PanykSystem/gameboy-hifi-audio/firmware/src/audio_pipeline.c

#include "audio_pipeline.h"

#include <stdbool.h>
#include <stdint.h>
#include <stdio.h>
#include <stdlib.h>
#include <string.h>
#include <math.h>

#include "freertos/FreeRTOS.h"
#include "freertos/stream_buffer.h"
#include "freertos/semphr.h"
#include "freertos/task.h"
#include "esp_log.h"
#include "esp_timer.h"

#include "dsps_fft2r.h"     // spectrum tap: esp-dsp radix-2 FFT

#include "i2s_codec.h"
#include "dsp.h"
#include "sfx.h"

#ifndef M_PI
#define M_PI 3.14159265358979323846
#endif

static const char *TAG = "audio";

// 256 stereo frames x 8 bytes/frame = 2 KB per read, ~5.8 ms at 44.1 kHz.
// Frequent small reads keep the producer/consumer relationship tight at the cost
// of more task wakeups per second.
#define READ_FRAMES 256
#define FRAME_BYTES 8                       // I2S input: stereo, 32-bit slots
#define OUT_FRAME_BYTES 4                   // PCM output: stereo, 16-bit

// At 44.1 kHz stereo 16-bit, audio is 176.4 KB/s (~176 bytes/ms). The stream
// buffer absorbs the BT consumer's burst pull pattern (it idles while L2CAP TX
// completes, then grabs a chunk). Sized to hold the ~5 KB natural burst swing
// (observed fill range 1-6 KB) plus a little margin above the high-water mark.
#define PCM_STREAM_BUFFER_BYTES (8 * 1024)     // ~46 ms max; was 12 KB
// High-water trim: the producer skips its push while the queue is already at/above
// this level, so latency stays bounded (~34 ms) instead of drifting toward full as
// the 44.1 kHz producer slowly outruns the sink's consume rate (no rate matching).
// Set above the ~5 KB burst swing so normal bursts aren't clipped -- only the slow
// drift trips it, dropping one ~6 ms block occasionally (rare, ~inaudible) rather
// than letting the fill climb to a 70 ms overflow.
#define PCM_STREAM_HIGH_WATER   (6 * 1024)
// Wake the BT consumer as soon as one SBC-sized block is ready.
// 512 bytes = 128 stereo frames ~2.9 ms.
#define PCM_STREAM_TRIGGER_LEVEL 512

#define MAG_LOG_INTERVAL_US 1000000          // peak log once per second

// On-demand ADC capture for noise-floor / spectrum analysis. audio_pipeline_capture()
// requests N raw samples; the pipeline grabs the next N frames verbatim (no arming, so
// it captures the quiet noise floor, not just loud audio) and dumps them as CSV between
// WAVEDUMP_BEGIN / WAVEDUMP_END markers over UART for tools/plot_wavedump.py. The dump
// printf stalls this real-time task ~1 s, so audio hiccups during a capture (fine for a
// bench measurement; the samples are already grabbed before the dump runs).
//
// The capture buffer is heap-allocated per request (by audio_pipeline_capture, in
// the caller's context) and freed by the pipeline task after the dump. A static
// buffer here would park 8 KB of DRAM for a bench-only feature -- DRAM the SBC
// encoder's 4 KB media buffers need at their tightest (streaming + a BLE config
// client + clip playback ran the heap dry and chopped the stream).
#define WAVEDUMP_MAX 1024                    // 23.2 ms at 44.1 kHz
static volatile int      s_wd_request = 0;   // samples to capture on next read (0 = idle)
static int32_t *volatile s_wd_buf     = NULL; // owned by the in-flight capture

static StreamBufferHandle_t s_pcm_stream = NULL;
// True only while a sink is actively streaming (set from bt_a2d on the media
// state). Gates the producer push so the buffer isn't pre-filled to full while
// idle/connecting. Written from the BT task, read by the pipeline task; a plain
// bool write is atomic on ESP32.
static volatile bool s_bt_streaming = false;

// Prebuffer: at stream start the consumer emits silence until this many bytes have
// queued, so real audio only flows once there's a cushion. Filling from empty
// otherwise underruns for the first ~0.5 s -- each partial read is real samples
// then zero-pad, a discontinuity the SBC encoder renders as garble. ~23 ms at
// 44.1 kHz/16-bit/stereo; small enough to stay low-latency, large enough to cover
// the consumer's bursty pull. Cleared on stop so each connect re-primes.
#define PCM_PRIME_TARGET_BYTES  (4 * 1024)
static volatile bool s_pcm_primed = false;

// Cooperative park (Mode A: stop the digital path so I2S/MCLK can stop).
// audio_pipeline_stop() sets s_park_req; the task acks via s_parked_sem at the
// top of its loop and blocks on a task notification until audio_pipeline_resume()
// wakes it. The task stays alive, so silence/peak window state and buffers
// persist, and I2S is never torn down under an in-flight read.
static TaskHandle_t      s_pipeline_task = NULL;
static SemaphoreHandle_t s_parked_sem    = NULL;
static volatile bool     s_park_req       = false;

// Silence detection state. Threshold is the int32 sample value: the ADC delivers
// 24-in-32 left-justified, so the int32 sample = 24-bit value << 8.
#define SILENCE_THRESHOLD_I32   0x10000
// Consecutive ~1 s below-threshold windows before declaring silence.
#define SILENCE_WINDOWS_TO_QUIET CONFIG_GBHIFI_SILENCE_WINDOWS

static audio_silence_cb_t s_silence_cb = NULL;
static bool s_is_silent = false;
static int  s_silent_window_count = 0;

// ---- spectrum tap ---------------------------------------------------------
// Per-channel rings of the newest post-DSP samples the user is hearing (the local
// speaker/HP program, or the Bluetooth program while a sink streams). The pipeline
// task fills them per block when enabled; audio_pipeline_compute_spectrum() (a
// non-realtime caller) snapshots the last SPEC_FFT_N of each and FFTs them
// independently for a stereo spectrum. Benign torn reads are fine for a
// visualizer, so the rings are lock-free.
#define SPEC_FFT_N    256                 // FFT window (5.8 ms at 44.1 kHz); small on
                                          // purpose to keep DRAM free for BT + BLE
#define SPEC_RING     512                 // >= SPEC_FFT_N, power of two
#define SPEC_MAX_BINS 64                  // per channel
static int16_t           s_spec_l[SPEC_RING];
static int16_t           s_spec_r[SPEC_RING];
static volatile uint32_t s_spec_wr    = 0;
static volatile bool     s_spec_on    = false;
static volatile bool     s_spec_is_bt = false;   // last tapped source: true=BT, false=local

void audio_pipeline_set_silence_cb(audio_silence_cb_t cb)
{
    s_silence_cb = cb;
}

// Load accounting (see audio_pipeline.h). Written only by the pipeline task;
// read + reset by the console. Plain aligned 32-bit accesses are atomic on
// ESP32; the 64-bit accumulator can tear against a concurrent reset, costing at
// worst one bench readout -- acceptable for diagnostics.
static volatile uint64_t s_ld_acc_us  = 0;
static volatile uint32_t s_ld_blocks  = 0;
static volatile uint32_t s_ld_max_us  = 0;
static volatile uint32_t s_ld_over    = 0;

void audio_pipeline_load_stats(audio_load_t *out)
{
    if (!out) return;
    uint32_t blocks = s_ld_blocks;
    out->blocks    = blocks;
    out->avg_us    = blocks ? (uint32_t)(s_ld_acc_us / blocks) : 0;
    out->max_us    = s_ld_max_us;
    out->over      = s_ld_over;
    out->budget_us = (uint32_t)((uint64_t)READ_FRAMES * 1000000u / 44100u);
    s_ld_acc_us = 0;
    s_ld_blocks = 0;
    s_ld_max_us = 0;
    s_ld_over   = 0;
}

void audio_pipeline_capture(int samples)
{
    if (samples <= 0 || samples > WAVEDUMP_MAX) samples = WAVEDUMP_MAX;
    if (s_wd_buf) return;   // a capture is already in flight; ignore
    // Allocated here (console-task context), freed by the pipeline task after
    // the dump. Failing is fine -- wavedump is a bench tool and the heap is
    // deliberately tight while streaming; try again with the stream stopped.
    int32_t *buf = malloc((size_t)samples * 2 * sizeof(int32_t));
    if (!buf) {
        printf("wavedump: not enough free heap (%d frames); stop streaming and retry\n",
               samples);
        return;
    }
    s_wd_buf = buf;
    s_wd_request = samples;
}

void audio_pipeline_spectrum_enable(bool on)
{
    s_spec_on = on;
}

bool audio_pipeline_spectrum_is_bt(void)
{
    return s_spec_is_bt;
}

// FFT one channel's ring snapshot into `nbins` log-spaced 0..255 magnitude bytes.
// `fft`/`hann` are caller-provided scratch/window (sized SPEC_FFT_N).
static void spec_channel(const int16_t *ring, float *fft, const float *hann,
                         uint8_t *out, int nbins)
{
    uint32_t start = s_spec_wr - SPEC_FFT_N;
    for (int i = 0; i < SPEC_FFT_N; i++) {
        float s = (float)ring[(start + i) & (SPEC_RING - 1)] * (1.0f / 32768.0f);
        fft[2 * i]     = s * hann[i];
        fft[2 * i + 1] = 0.0f;
    }
    dsps_fft2r_fc32(fft, SPEC_FFT_N);
    dsps_bit_rev_fc32(fft, SPEC_FFT_N);

    // Fold bins 1..N/2 into nbins log-spaced bands (peak power per band), then map
    // dB to a 0..255 byte. Rough by design -- it's a "cool" meter, not analysis.
    const int   kmax     = SPEC_FFT_N / 2;      // 256
    const float FLOOR_DB = -60.0f;
    for (int b = 0; b < nbins; b++) {
        int lo = (int)floorf(powf((float)kmax, (float)b / nbins));
        int hi = (int)floorf(powf((float)kmax, (float)(b + 1) / nbins));
        if (lo < 1)    lo = 1;
        if (hi <= lo)  hi = lo + 1;
        if (hi > kmax) hi = kmax;
        float peak = 0.0f;
        for (int k = lo; k < hi; k++) {
            float re = fft[2 * k], im = fft[2 * k + 1];
            float p = re * re + im * im;        // power (magnitude^2)
            if (p > peak) peak = p;
        }
        float norm = peak / ((float)kmax * (float)kmax);
        float db   = 10.0f * log10f(norm + 1e-9f);   // 10*log10: norm is power
        int   v    = (int)((db - FLOOR_DB) / (0.0f - FLOOR_DB) * 255.0f);
        if (v < 0)   v = 0;
        if (v > 255) v = 255;
        out[b] = (uint8_t)v;
    }
}

int audio_pipeline_compute_spectrum(uint8_t *bins, int nbins)
{
    if (!s_spec_on || !bins || nbins <= 0) return 0;
    if (nbins > SPEC_MAX_BINS) nbins = SPEC_MAX_BINS;

    static bool  s_ready = false;
    static float s_hann[SPEC_FFT_N];
    static float s_fft[SPEC_FFT_N * 2];         // reused L then R (sequential)
    if (!s_ready) {
        if (dsps_fft2r_init_fc32(NULL, SPEC_FFT_N) != ESP_OK) {
            ESP_LOGW(TAG, "fft init failed; spectrum disabled");
            s_spec_on = false;
            return 0;
        }
        for (int i = 0; i < SPEC_FFT_N; i++)
            s_hann[i] = 0.5f * (1.0f - cosf(2.0f * (float)M_PI * i / (SPEC_FFT_N - 1)));
        s_ready = true;
    }

    spec_channel(s_spec_l, s_fft, s_hann, bins,         nbins);  // L bands
    spec_channel(s_spec_r, s_fft, s_hann, bins + nbins, nbins);  // R bands
    return 2 * nbins;
}

void audio_pipeline_set_bt_streaming(bool streaming)
{
    s_bt_streaming = streaming;
    if (!streaming) s_pcm_primed = false;   // re-prebuffer on the next connect
}

bool audio_pipeline_is_silent(void)
{
    return s_is_silent;
}

static void update_silence(int32_t peak_max)
{
    bool below = (peak_max < SILENCE_THRESHOLD_I32);
    if (below) {
        if (s_silent_window_count < SILENCE_WINDOWS_TO_QUIET) {
            s_silent_window_count++;
        }
        if (!s_is_silent && s_silent_window_count >= SILENCE_WINDOWS_TO_QUIET) {
            s_is_silent = true;
            if (s_silence_cb) s_silence_cb(true);
        }
    } else {
        s_silent_window_count = 0;
        if (s_is_silent) {
            s_is_silent = false;
            if (s_silence_cb) s_silence_cb(false);
        }
    }
}

static void pipeline_task(void *arg)
{
    // The ES8388 ADC emits 24-bit samples in 32-bit I2S slots (32-in-32), so
    // each int32 holds the 24-bit sample value in bits 31:8, zero-pad in 7:0. A
    // sign-extending right-shift by 16 gives a 16-bit signed value, discarding
    // the 8 least-significant bits of resolution.
    static int32_t stereo_buf[READ_FRAMES * 2];     // ADC in: int32 L,R
    static int16_t out_buf[READ_FRAMES * 2];        // BT PCM out: int16 L,R interleaved
    static int16_t local_buf[READ_FRAMES * 2];      // local DAC program: int16 L,R interleaved (stereo)
    static int32_t dac_buf[READ_FRAMES * 2];        // DAC out: int32 L,R (stereo)

    int32_t peak_l = 0, peak_r = 0;
    size_t  fill_min = SIZE_MAX, fill_max = 0;
    int64_t window_start_us = esp_timer_get_time();
    // On-demand capture buffer (filled across reads, one read is only READ_FRAMES).
    // Heap-allocated per capture by audio_pipeline_capture(); freed here after the
    // dump so the 8 KB isn't resident between bench captures.
    int32_t *wd_buf = NULL;
    int wd_have = 0;      // samples captured into the active dump
    int wd_target = 0;    // 0 = not capturing; else samples requested for this dump
    bool bt_streaming_prev = false;   // edge-detect the streaming gate for buffer reset

    while (1) {
        // Cooperative park for Mode A: when stop() requests it, ack and block
        // until resume() notifies us. Done at the loop top so we are not inside
        // i2s_codec_read when the channel is disabled. On wake, I2S has already
        // been restarted by resume(), so fall through to the next read.
        if (s_park_req) {
            s_park_req = false;
            xSemaphoreGive(s_parked_sem);
            ulTaskNotifyTake(pdTRUE, portMAX_DELAY);
            continue;
        }

        size_t bytes_read = 0;
        esp_err_t err = i2s_codec_read(stereo_buf, sizeof(stereo_buf), &bytes_read, 100);
        if (err != ESP_OK) {
            ESP_LOGW(TAG, "i2s read: %s (bytes=%u)",
                     esp_err_to_name(err), (unsigned)bytes_read);
            vTaskDelay(pdMS_TO_TICKS(100));
            continue;
        }

        size_t frames = bytes_read / FRAME_BYTES;
        int64_t work_t0 = esp_timer_get_time();

        // On-demand capture: when a request lands, grab the next wd_target frames
        // verbatim (no arming, so the quiet noise floor is captured as-is), then dump
        // as CSV between markers. printf (not ESP_LOG) so the host parser gets clean
        // lines. The dump stalls this task ~1 s; audio hiccups then recovers.
        if (wd_target == 0 && s_wd_request > 0) {
            wd_target = s_wd_request;
            s_wd_request = 0;
            wd_buf = s_wd_buf;
            wd_have = 0;
        }
        if (wd_target > 0 && wd_buf) {
            for (size_t i = 0; i < frames && wd_have < wd_target; i++) {
                wd_buf[wd_have * 2]     = stereo_buf[i * 2];
                wd_buf[wd_have * 2 + 1] = stereo_buf[i * 2 + 1];
                wd_have++;
            }
            if (wd_have >= wd_target) {
                printf("WAVEDUMP_BEGIN n=%d fs=44100 fmt=24in32\n", wd_target);
                for (int i = 0; i < wd_target; i++) {
                    printf("%ld,%ld\n",
                           (long)wd_buf[i * 2], (long)wd_buf[i * 2 + 1]);
                }
                printf("WAVEDUMP_END\n");
                wd_target = 0;
                free(wd_buf);
                wd_buf = NULL;
                s_wd_buf = NULL;   // capture complete; allow the next request
            }
        }

        // Convert stereo 32-bit slot data to 16-bit interleaved stereo, tracking
        // peaks for the once-per-second magnitude log. The sign-extending
        // right-shift by 16 keeps the 16 most significant bits of the 24-bit
        // sample, discarding the lowest 8 bits of resolution.
        for (size_t i = 0; i < frames; i++) {
            int32_t l = stereo_buf[i * 2];
            int32_t r = stereo_buf[i * 2 + 1];

            int32_t la = (l < 0) ? -l : l;
            int32_t ra = (r < 0) ? -r : r;
            if (la > peak_l) peak_l = la;
            if (ra > peak_r) peak_r = ra;

            int16_t lo = (int16_t)(l >> 16);
            int16_t ro = (int16_t)(r >> 16);
            out_buf[i * 2]     = lo;
            out_buf[i * 2 + 1] = ro;
            // Local program stays stereo. The ES8388 DAC drives the HP amp
            // (LOUT1/ROUT1) directly, which must stay stereo, and the line out
            // (LOUT2/ROUT2) feeds a passive 2-R L+R sum to the mono speaker amp.
            // The speaker mono-down happens in hardware, not here.
            local_buf[i * 2]     = lo;
            local_buf[i * 2 + 1] = ro;
        }

        // Render this block's SFX cue once (advances cue state a single time) so
        // the same samples can be mixed into both the BT and DAC paths.
        sfx_generate_block(frames);

        // BT DSP: source-side noise reduction (HPF/LPF/notch + gate) + optional EQ
        // + digital volume + SFX cue mix, in place on out_buf before the
        // stream-buffer push so the SBC encoder sees the cleaned, gated signal (not
        // the raw capture floor, which SBC renders as audible digital hash).
        //
        // Run it only while a sink is actually streaming: the push below is gated
        // on s_bt_streaming, so outside of streaming the processed buffer is
        // thrown away and the NR chain (a dozen biquad passes since the
        // reconstruction LPF) is pure waste. At 80 MHz that waste was real: it
        // left the boot chime's blocks over budget while the boot-time init
        // storm ran, which chopped the chime. On the idle->streaming edge the BT
        // DSP state (filter delay lines, gate envelope) is stale from the last
        // stream, so reset it for a clean start.
        bool bt_streaming = s_bt_streaming;
        if (bt_streaming) {
            if (!bt_streaming_prev) dsp_bt_reset();
            dsp_process_bt(out_buf, frames);
        }

        // Push the interleaved stereo PCM into the stream buffer for A2DP, but only
        // while a sink is actively streaming. Gating the fill keeps the buffer from
        // pre-filling to full while idle/connecting -- which otherwise hands the SBC
        // encoder a full (~70 ms) buffer at connect that overflows and drops for a
        // second or two. On the streaming->idle edge, empty the buffer so the next
        // connect starts from ~0 latency; the consumer (a2d_data_cb) is idle once the
        // media stops, so the reset does not race a concurrent read. Non-blocking
        // send: if the consumer falls behind, drop rather than stall I2S DMA.
        if (s_pcm_stream && bt_streaming) {
            // High-water trim: skip the push while the queue is already at the mark,
            // so latency stays bounded instead of drifting toward full. Drops the
            // newest ~6 ms block once per drift accumulation (rare) rather than
            // letting the fill climb to an eventual overflow.
            if (xStreamBufferBytesAvailable(s_pcm_stream) < PCM_STREAM_HIGH_WATER) {
                (void)xStreamBufferSend(s_pcm_stream, out_buf,
                                        frames * OUT_FRAME_BYTES, 0);
            }
            size_t fill = xStreamBufferBytesAvailable(s_pcm_stream);
            if (fill < fill_min) fill_min = fill;
            if (fill > fill_max) fill_max = fill;
        } else if (s_pcm_stream && bt_streaming_prev && !bt_streaming) {
            xStreamBufferReset(s_pcm_stream);   // streaming ended: drop stale audio
        }
        // (bt_streaming_prev is updated at the end of the loop iteration: the
        // DAC-zeroing block below also needs to see the idle->streaming edge.)

        // Local DSP: stereo speaker EQ, digital volume, SFX cue mix, saturate,
        // in place on the interleaved local buffer.
        //
        // Skipped entirely while a sink streams: STREAMING and local playback are
        // mutually exclusive (the state machine mutes the speaker amp for the whole
        // stream, and a wired HP plug suspends A2DP), so the local program is
        // computed only to be played into muted/disconnected outputs. At 80 MHz
        // that waste is what starves core 0's SBC encoder of its escape hatch:
        // dropping it frees the core-1 headroom the relocated BT controller task
        // needs (see CONFIG_BTDM_CTRL_PINNED_TO_CORE_1 in sdkconfig.defaults).
        // The gate/amp-mute state simply freezes for the duration; app_sm's
        // stream-wide amp mute owns the speaker while streaming, and the gate
        // resumes from its pre-stream state when the stream ends.
        if (!bt_streaming) {
            dsp_process_local(local_buf, frames);
        }

        // Spectrum tap: mirror the *post-DSP* output the user is actually hearing
        // into the rings so the web visualizer reflects live EQ/volume/SFX. Follow
        // the active path: the Bluetooth program (out_buf, post BT DSP) while a sink
        // is streaming, else the local speaker/HP program (local_buf, post local DSP).
        if (s_spec_on) {
            const int16_t *src = bt_streaming ? out_buf : local_buf;
            s_spec_is_bt = bt_streaming;
            uint32_t wr = s_spec_wr;
            for (size_t i = 0; i < frames; i++) {
                s_spec_l[wr & (SPEC_RING - 1)] = src[i * 2];
                s_spec_r[wr & (SPEC_RING - 1)] = src[i * 2 + 1];
                wr++;
            }
            s_spec_wr = wr;
        }

        // Fan the processed program out to the ES8388 DAC in stereo (sample value
        // in bits 31:8 to match the ADC framing). The DAC drives the HP amp (true
        // stereo) plus the line out to the passive L+R sum and mono speaker amp,
        // which the state machine's mute policy gates (silent during BT streaming
        // and while wired HP is plugged). Same clock domain as the RX read, so
        // writing the same frame count keeps the bus balanced.
        //
        // While a sink streams, the local outputs are muted/unplugged and
        // dsp_process_local was skipped, so drive the DAC with zeros instead of
        // the raw un-volumed capture: one memset on the edge, then the buffer
        // stays zero (the loop below is skipped). The write itself stays -- it
        // paces the TX side and keeps the bus balanced.
        if (!bt_streaming) {
            for (size_t i = 0; i < frames; i++) {
                dac_buf[i * 2]     = (int32_t)local_buf[i * 2]     << 16;
                dac_buf[i * 2 + 1] = (int32_t)local_buf[i * 2 + 1] << 16;
            }
        } else if (!bt_streaming_prev) {
            memset(dac_buf, 0, sizeof(dac_buf));
        }
        bt_streaming_prev = bt_streaming;
        // Load accounting: compute time for this block (read-return to DAC
        // hand-off; the blocking read/write are pacing, not load). The budget is
        // the block's real-time length. Wavedump blocks are excluded -- the CSV
        // printf stall is a deliberate bench action, not pipeline load.
        if (wd_target == 0) {
            uint32_t work_us   = (uint32_t)(esp_timer_get_time() - work_t0);
            uint32_t budget_us = (uint32_t)((uint64_t)frames * 1000000u / 44100u);
            s_ld_acc_us += work_us;
            s_ld_blocks++;
            if (work_us > s_ld_max_us) s_ld_max_us = work_us;
            if (work_us > budget_us)   s_ld_over++;
        }

        size_t dac_written = 0;
        (void)i2s_codec_write(dac_buf, frames * FRAME_BYTES, &dac_written, 100);

        int64_t now_us = esp_timer_get_time();
        if (now_us - window_start_us >= MAG_LOG_INTERVAL_US) {
#if CONFIG_GBHIFI_DEBUG_PEAK_LOG
            // Opt-in per-second ADC level readout for gain/clip checks. Default
            // off (ESP_LOGD), compiled out at the INFO log level.
            ESP_LOGI(TAG, "peak L=0x%08lx R=0x%08lx  buf=%u-%u/%u B",
#else
            ESP_LOGD(TAG, "peak L=0x%08lx R=0x%08lx  buf=%u-%u/%u B",
#endif
                     (unsigned long)peak_l, (unsigned long)peak_r,
                     (unsigned)fill_min, (unsigned)fill_max,
                     (unsigned)PCM_STREAM_BUFFER_BYTES);
            update_silence((peak_l > peak_r) ? peak_l : peak_r);
            peak_l = 0;
            peak_r = 0;
            fill_min = SIZE_MAX;
            fill_max = 0;
            window_start_us = now_us;
        }
    }
}

esp_err_t audio_pipeline_start(void)
{
    if (!s_pcm_stream) {
        s_pcm_stream = xStreamBufferCreate(PCM_STREAM_BUFFER_BYTES,
                                           PCM_STREAM_TRIGGER_LEVEL);
        if (!s_pcm_stream) {
            return ESP_ERR_NO_MEM;
        }
    }

    if (!s_parked_sem) {
        s_parked_sem = xSemaphoreCreateBinary();
        if (!s_parked_sem) {
            return ESP_ERR_NO_MEM;
        }
    }

    // 4 KB stack: the large buffers are static, so the task mainly needs space
    // for the i2s driver call chain and printf inside the wavedump block.
    // Priority 10 to preempt user-priority tasks and keep the producer/consumer
    // hand-off tight.
    //
    // Pinned to core 1 (APP_CPU): the BT controller + Bluedroid are pinned to
    // core 0. During A2DP streaming that BT work would otherwise preempt this
    // producer for 20-26 ms at a time on a shared core, underrunning the A2DP
    // stream and garbling BT. The other core isolates the audio producer from BT
    // preemption.
    BaseType_t ok = xTaskCreatePinnedToCore(pipeline_task, "audio_pipe",
                                            4096, NULL, 10, &s_pipeline_task, 1);
    return (ok == pdPASS) ? ESP_OK : ESP_FAIL;
}

esp_err_t audio_pipeline_stop(void)
{
    if (!s_pipeline_task || !s_parked_sem) return ESP_ERR_INVALID_STATE;
    // Ask the task to park, then wait for its ack before stopping I2S so the
    // channel is never disabled under an in-flight i2s_channel_read. The read
    // timeout is 100 ms, so the task parks within one read; allow generous slack.
    s_park_req = true;
    if (xSemaphoreTake(s_parked_sem, pdMS_TO_TICKS(500)) != pdTRUE) {
        ESP_LOGW(TAG, "pipeline did not park in time");
        s_park_req = false;
        return ESP_ERR_TIMEOUT;
    }
    esp_err_t err = i2s_codec_stop();
    ESP_LOGI(TAG, "pipeline stopped (I2S off): %s", esp_err_to_name(err));
    return err;
}

esp_err_t audio_pipeline_resume(void)
{
    if (!s_pipeline_task) return ESP_ERR_INVALID_STATE;
    // Fully rebuild the I2S bus before un-parking the task. A bare
    // i2s_codec_start() (re-enable) is not enough after audio_pipeline_stop():
    // when Mode A light-sleeps the CPU, the APLL that feeds MCLK/BCLK is powered
    // down, and re-enabling the channels against it yields wrong clocks. The ADC
    // read then returns un-paced (the task spins, starving the core-1 idle task
    // and tripping the task-WDT) and the audio is garbled. Delete + recreate
    // re-locks the APLL from scratch. The ES8388 keeps its registers across this
    // (separately powered), so no re-config is needed; the caller re-asserts DSP
    // mode after.
    i2s_codec_deinit();
    esp_err_t err = i2s_codec_init();
    if (err != ESP_OK) {
        ESP_LOGE(TAG, "i2s reinit failed: %s", esp_err_to_name(err));
        return err;
    }
    err = i2s_codec_start();
    if (err != ESP_OK) {
        ESP_LOGE(TAG, "i2s restart failed: %s", esp_err_to_name(err));
        return err;
    }
    xTaskNotifyGive(s_pipeline_task);
    ESP_LOGI(TAG, "pipeline resumed (I2S rebuilt)");
    return ESP_OK;
}

size_t audio_pipeline_read_stereo16(void *dst, size_t max_bytes,
                                    uint32_t timeout_ms)
{
    if (!s_pcm_stream || !dst || max_bytes == 0) {
        return 0;
    }
    // Prebuffer at stream start: hold real audio back until a cushion has built. A
    // 0-length return makes the A2DP callback emit clean silence; once the queue
    // reaches the target we latch primed and stream normally. Re-primes on the next
    // connect (the gate clears s_pcm_primed on stop).
    if (!s_pcm_primed) {
        if (xStreamBufferBytesAvailable(s_pcm_stream) < PCM_PRIME_TARGET_BYTES) {
            return 0;
        }
        s_pcm_primed = true;
    }
    return xStreamBufferReceive(s_pcm_stream, dst, max_bytes,
                                pdMS_TO_TICKS(timeout_ms));
}
