PanykSystem/gameboy-hifi-audio/firmware/src/settings.h

#pragma once

#include <stdbool.h>
#include <stdint.h>

#include "esp_err.h"

// Runtime-tunable DSP parameters.
//
// Single source of truth for everything a control surface (serial console, web
// UI) can change. Those surfaces only call the settings_* API here; they never
// touch the audio path. The DSP engine (dsp.c) is a pure consumer: it takes a
// snapshot per block and recomputes filter coefficients only when `generation`
// changes.
//
// Persisted as a single versioned blob in NVS (namespace "gbhifi_cfg", key
// "dsp"). Bump GBHIFI_SETTINGS_VERSION when the struct layout changes; an
// older/absent blob falls back to the Kconfig-seeded defaults.

#define GBHIFI_SETTINGS_VERSION 14

// Which boot chime the mod voices on a genuine power-on. Clip modes stream
// /clips/<name>.gsfx; STARTUP_OFF plays nothing and leaves the live GBA
// passthrough unmuted. OFF is not ORIGINAL: the codec and amp are still coming
// up for the GBA's first ~0.9 s, so the passthrough chime is truncated.
// Values are persisted; append only, never renumber.
typedef enum {
    STARTUP_MODERN   = 0,  // startup-modern.gsfx: the Switch/NSO version (default)
    STARTUP_ORIGINAL = 1,  // startup-original.gsfx: the full original GBA chime
    STARTUP_CUSTOM   = 2,  // startup-custom.gsfx: the user's uploaded slot
    STARTUP_OFF      = 3,  // no clip; the live GBA chime plays through untouched
    STARTUP_MODE_COUNT,
} startup_mode_t;

// Clip base name for a startup_mode_t (as passed to sfx_trigger_clip), or NULL
// for STARTUP_OFF and any unknown value, so a forward-version NVS blob cannot
// voice the wrong chime.
const char *settings_startup_clip(uint8_t mode);

// Battery chemistry. Selects the discharge-curve model the battery meter maps
// VBAT through (each chemistry droops differently under load), and the nominal
// series resistance used for load compensation. The single user-facing accuracy
// knob for the meter; everything else is derived. Default ALKALINE matches a
// stock 2xAA GBA and the historical linear curve. Values are persisted; append
// only, never renumber.
typedef enum {
    BATT_CHEM_ALKALINE = 0,  // 2xAA alkaline: ~3.2 V fresh, near-linear to ~2.0 V
    BATT_CHEM_NIMH     = 1,  // 2xAA NiMH: long 2.4-2.5 V plateau, then a fast knee
    BATT_CHEM_LIPO_REG = 2,  // regulated LiPo mod: flat ~3.0-3.2 V until dropout
    BATT_CHEM_COUNT,
} batt_chem_t;

typedef struct {
    uint16_t version;          // == GBHIFI_SETTINGS_VERSION
    uint8_t  speaker_vol_pct;  // local-speaker digital volume, 0..100
    uint8_t  bt_vol_pct;       // Bluetooth digital volume, 0..100 (100 = unity)

    // Speaker EQ (local DAC path while no headphones are plugged). Voices the
    // small GBA driver (bass roll-off + presence). 3 bands, gains in dB, -12..+12.
    bool     eq_enabled;
    int8_t   eq_bass_db;       // low-shelf  ~150 Hz
    int8_t   eq_mid_db;        // peak       ~2.5 kHz
    int8_t   eq_treble_db;     // high-shelf ~5 kHz

    // Headphone EQ (same local DAC path, but the profile used while wired
    // headphones are plugged). One DSP chain feeds the ES8388 DAC, which drives
    // either the speaker (HP out) or the HP amp (HP in), never both at once
    // (pam_apply mutes the speaker when HP is plugged), so app_sm swaps which
    // gain set the EQ uses on the HP-detect edge (dsp_set_hp_plugged). Off by
    // default with flat gains. Same 3 bands/freqs.
    bool     eq_hp_enabled;
    int8_t   eq_hp_bass_db;
    int8_t   eq_hp_mid_db;
    int8_t   eq_hp_treble_db;

    // Bluetooth EQ (A2DP path). Off by default; an optional source-side tone
    // control. Same 3 bands/freqs as the speaker, independent gains. Applied in
    // stereo before the SBC encoder.
    bool     eq_bt_enabled;
    int8_t   eq_bt_bass_db;
    int8_t   eq_bt_mid_db;
    int8_t   eq_bt_treble_db;

    bool     sfx_enabled;      // allow cues (chimes/clips) to mix in (speaker only)
    int8_t   sfx_level_db;     // cue mix gain trim, -24..+6 dB (0 = authored)
    // Which boot chime to voice (startup_mode_t). Independent of sfx_enabled,
    // which gates ALL cues: with cues off no startup clip plays regardless of
    // this. main.c reads it once at boot.
    uint8_t  startup_mode;

    // ---- Noise reduction (local capture path) ----
    // Tunable per GBA: board revision and other mods change the noise floor. Each
    // is a biquad applied to the captured signal before the EQ; 0 Hz disables that
    // filter. Use the `wavedump` capture + tools/plot_wavedump.py to find the tones.
    uint16_t nr_hpf_hz;        // high-pass corner: low-frequency hum
    uint16_t nr_lpf_hz;        // low-pass corner: high-frequency hiss
    // LPF slope as Butterworth order (2, 4, or 6 = 12/24/36 dB per octave).
    // Steeper orders approximate a proper reconstruction filter for the GBA's
    // nearest-neighbor resampling images: game PCM runs at ~10-21 kHz, so
    // everything above that source's Nyquist is aliasing, not program. 2 keeps
    // the historical gentle hiss roll-off.
    uint8_t  nr_lpf_order;
    uint16_t nr_notch_hz;      // notch center: a discrete tone (e.g. aliased PWM carrier)
    uint8_t  nr_notch_q;       // notch Q (sharpness); higher = narrower
    // Downward expander / noise gate: when the program level falls below
    // nr_gate_thresh_db it is attenuated toward -nr_gate_range_db, so the noise
    // floor fades out in quiet passages (kills "worst when silent"). 0 dBFS = off.
    int8_t   nr_gate_thresh_db; // threshold, dBFS (0 = off; else negative)
    uint8_t  nr_gate_range_db;  // max attenuation when fully closed, dB
    // Bluetooth-only hard mute: sustained below this RMS (dBFS) the A2DP program
    // is driven to true digital zero, so the SBC encoder sees real silence instead
    // of rendering the low-level floor as hash. More aggressive than the shared
    // expander above; BT-path only (the local analog path tolerates a low floor).
    // 0 = off (no hard mute; the expander still runs). Set below the gate
    // threshold to hard-mute only true silence and let quiet program through.
    int8_t   nr_bt_mute_db;

    // ---- Operating-mode preferences ----
    // Sticky user choice of audio path. app_sm owns the actual transition; a
    // control surface (console / BLE) only flips this flag and app_sm reacts.
    //   false = Mode B (full DSP: EQ/SFX/volume + A2DP, ES8388 ADC to DAC)
    //   true  = Mode A (analog bypass: ES8388 LIN to outputs, digital path stopped)
    bool     mode_a;
    // Whether the Mode A/B preference (mode_a) survives a power cycle. true
    // (default) = sticky: if powered off in Mode A, boot back into Mode A (after
    // the startup chime window, unless the CP button is held at power-on or the
    // `bootb` console command cancels it). false = Mode A is session-only: every
    // boot comes up in Mode B local regardless of how it was powered off.
    bool     boot_mode_a;
    // Bluetooth connect-on-boot policy. false (default) = manual: the radio comes
    // up idle and the device waits in LOCAL_ONLY; no page/inquiry happens until
    // the user holds the Connect/Pair (R) button to start it. true = auto: on
    // boot, immediately re-page bonded sinks (or enter pairing if none bonded),
    // the legacy behavior. app_sm reads this at boot; a control surface only
    // flips the flag.
    bool     auto_connect;

    // Battery chemistry (batt_chem_t). Selects the meter's discharge curve +
    // nominal load-compensation resistance. app_sm reads it each battery poll.
    uint8_t  batt_chem;

    // ---- R-button hold-menu thresholds (ms) ----
    // The Connect/Pair (R) button drives a chime-guided hold menu: held past
    // each threshold the device chimes that rung; release in a zone runs its
    // action. Runtime-tunable so the user can lengthen/shorten the gesture (R is
    // mashed during gameplay). Defaults seed from Kconfig. Absolute thresholds
    // from press, strictly increasing: connect <= pair <= mode. buttons.c reads
    // these; sanitise() enforces order.
    uint16_t hold_connect_ms;   // release >= here, < pair: connect bonded
    uint16_t hold_pair_ms;      // release >= here, < mode: pairing
    uint16_t hold_mode_ms;      // release >= here:         toggle Mode A/B
    // Plain hold to leave Mode A (no menu, since the DSP/SFX path is stopped in
    // bypass so the menu chimes can't play). Timed by app_sm's light-sleep loop.
    uint16_t hold_mode_exit_ms;
} gbhifi_settings_t;

// Load the blob from NVS, or seed Kconfig defaults if absent / older version.
// Idempotent; safe to call once at boot before the audio pipeline starts.
esp_err_t settings_init(void);

// Copy the current settings under lock. Cheap; the audio task calls this once
// per ~5.8 ms block. Always returns a fully-populated, validated struct.
void settings_get(gbhifi_settings_t *out);

// Monotonic counter, bumped on every successful setter. Lets a consumer cheaply
// detect "params changed" without diffing the struct. Plain aligned 32-bit
// read, atomic on ESP32, no lock needed.
uint32_t settings_generation(void);

// Setters: validate/clamp, update the master copy under lock, bump generation.
// Do NOT auto-persist (flash wear); call settings_commit() to save.
esp_err_t settings_set_volume(uint8_t pct);
esp_err_t settings_set_bt_volume(uint8_t pct);
esp_err_t settings_set_eq(bool enabled, int8_t bass_db, int8_t mid_db, int8_t treble_db);
esp_err_t settings_set_hp_eq(bool enabled, int8_t bass_db, int8_t mid_db, int8_t treble_db);
esp_err_t settings_set_bt_eq(bool enabled, int8_t bass_db, int8_t mid_db, int8_t treble_db);
esp_err_t settings_set_sfx(bool enabled, int8_t level_db);
// Select the boot chime. Out-of-range values fall back to STARTUP_MODERN.
esp_err_t settings_set_startup_mode(uint8_t mode);
esp_err_t settings_set_nr(uint16_t hpf_hz, uint16_t lpf_hz, uint16_t notch_hz,
                          uint8_t notch_q);
// Set the LPF slope (Butterworth order 2/4/6; odd/out-of-range values snap to
// the nearest legal order).
esp_err_t settings_set_nr_lpf_order(uint8_t order);
esp_err_t settings_set_nr_gate(int8_t thresh_db, uint8_t range_db);
// Set the Bluetooth hard-mute threshold (dBFS, <= 0; 0 = off).
esp_err_t settings_set_nr_bt_mute(int8_t db);
esp_err_t settings_set_mode_a(bool mode_a);
esp_err_t settings_set_boot_mode_a(bool boot_mode_a);
esp_err_t settings_set_auto_connect(bool auto_connect);
// Select the battery chemistry (batt_chem_t). Out-of-range falls back to ALKALINE.
esp_err_t settings_set_chemistry(uint8_t chem);
// Set the R-button hold-menu thresholds (ms). Clamped + re-ordered so
// connect <= pair <= mode (sanitise()). mode_exit is independent.
esp_err_t settings_set_hold_timings(uint16_t connect_ms, uint16_t pair_ms,
                                    uint16_t mode_ms, uint16_t mode_exit_ms);

// Persist the current settings to NVS. Explicit (not per-set) to bound wear.
esp_err_t settings_commit(void);
