PanykSystem/gameboy-hifi-audio/firmware/src/app_sm.h

#pragma once

#include <stdbool.h>
#include <stdint.h>

#include "esp_err.h"

// Top-level state machine. Owns transitions between DEEP_IDLE, STANDBY,
// PAIRING, CONNECTED_IDLE, and STREAMING. Subscribes to buttons, bt_a2d, and
// audio_pipeline events and drives connection attempts, pairing entry, A2DP
// media start/suspend, and the speaker amp mute via PIN_PAM_SD.
//
// Call after buttons_init / audio_pipeline_start / bt_a2d_init have all
// returned ESP_OK. Boots directly into STANDBY.
esp_err_t app_sm_start(void);

// Bring the local-speaker amp up early, before the BT stack init + app_sm_start()
// that would otherwise gate it seconds out. Samples HP-detect and applies the same
// HP-aware rule as steady state: speaker amp on only when no headphones are plugged
// (the ES8388 DAC feeds both outputs, so with HP in the speaker must stay muted).
// Lets the Game Boy power-on chime play the earliest possible moment without
// clipping. Idempotent with the pam_init() inside app_sm_start(), which re-evaluates
// the amp against the live HP/gate/STREAMING state.
void app_sm_speaker_early_on(void);

// Bring up the VOL-wheel ADC and seed the speaker volume from the wheel before the
// audio pipeline produces its first block, so boot audio starts at the wheel
// setting rather than the stored default (which otherwise blares for a wheel-down
// user until app_sm_start()'s poll — now behind the BT hold-off — first runs).
// Call after settings_init() and before dsp_init(). Idempotent with the ADC init
// inside app_sm_start().
void app_sm_prime_volume(void);

// The HP-detect state sampled by app_sm_speaker_early_on() (true = headphones
// plugged). Lets boot bring-up seed the DSP's HP-vs-speaker EQ profile before the
// first audio block, so the startup chime is voiced for the live output. Valid only
// after app_sm_speaker_early_on(); sm_task re-samples the live pin once it runs.
bool app_sm_hp_plugged(void);

// Boot-time radio-inrush mute window. `quiet=true` forces the speaker amp SD low
// regardless of policy; `quiet=false` re-applies the normal HP/state rule. Used by
// main.c around the BT controller enable: the radio's PHY-calibration current
// spike plus a loud speaker peak can sag the boost rail below the brownout
// threshold on a low battery, so the amp is parked for that window. Only
// meaningful between app_sm_speaker_early_on() and app_sm_start() (later, the
// state machine owns the pin and re-applies policy on its own events).
void app_sm_amp_radio_quiet(bool quiet);

// Bench/console: post the same state-machine events a Connect/Pair button hold
// releases (connect zone / pair zone), so BT reconnect and pairing can be driven
// from the serial or BLE console without touching the physical button. No-ops
// (with a warning) before app_sm_start(). The state machine applies its normal
// per-state rules, so e.g. a connect request in PAIRING is ignored just as a
// button release would be.
void app_sm_request_bt_connect(void);
void app_sm_request_bt_pair(void);

// Test/debug: force an immediate transition to DEEP_IDLE (ESP32 deep sleep) from
// any awake state except PAIRING. Used by the `sleep` console command for
// deep-sleep/wake reliability cycling. Wake sources are configured exactly as in
// a normal DEEP_IDLE entry: R-button (EXT1, held) or an HP-detect edge (EXT0).
void app_sm_request_sleep(void);

// Switch operating mode by rebooting into it (Mode A boots BT-less for power +
// reliability; Mode B boots with the radio). Persists the mode, then esp_restart().
// Does not return. No-op if already in the requested mode.
void app_sm_switch_mode(bool to_mode_a);

// Hand app_sm the boot-mode decision main.c already made (so it drops into the
// same mode it skipped/kept BT init for). Call before app_sm_start().
void app_sm_set_boot_into_mode_a(bool v);

// Enable/disable the VOL-wheel poll driving volume (GPIO39 ADC). The mode-change
// poll still runs either way; this only gates whether the wheel reading is
// applied to volume. Defaults ON: the wheel is the GBA's physical volume control.
// `wheel off` (console) disables it when the console `vol` should win, or when the
// wheel is physically disconnected. In Mode B the wheel sets the local-speaker DSP
// volume; in Mode A it sets the ES8388 output drivers.
void app_sm_set_wheel_enabled(bool enabled);

// Raw ADC floor below which the VOL line reads open rather than turned down. The
// wheel is a VBAT-referenced divider, so its wiper cannot reach ground while
// connected (calibrated floor ~330); a disconnected line measures ~16. Shared
// with harness.c so both use one number.
#define APP_SM_VOL_OPEN_RAW 150

// True when the VOL wheel line reads open. Costs one oversampled ADC read.
bool app_sm_vol_line_open(void);

// Diagnostic: sample the VOL wheel right now. *raw_out gets the 12-bit ADC value
// (-1 if the ADC is unavailable), *pct_out gets the mapped 0..100. The wheel is
// VCC-referenced (ratiometric), so the top of travel reads below full-scale and
// drifts with the battery; use this from the `wheel` console command to
// characterise the real min/max for calibration.
void app_sm_vol_wheel_read(int *raw_out, int *pct_out);

// Debug/bench: override HP-detect so a test doesn't require physically holding
// the jack. mode: 1 = force plugged, 0 = force unplugged, -1 = follow the real
// GPIO again. While forced, real jack edges are ignored. Driven by the
// `hp plug|unplug|follow` console command.
void app_sm_force_hp(int mode);

// Battery sense on ADC1_CH0 (VBAT through the R20/R21 = 100k/100k divider, so
// VBAT = 2x the sensed voltage). app_sm_read_vbat_mv returns the raw (loaded)
// VBAT in millivolts, -1 if the sense/cali is unavailable. The volume wheel is
// battery-referenced off the same VBAT so its calibration holds as it droops.
int  app_sm_read_vbat_mv(void);

// Battery meter band: a chemistry-independent 4-level state the meter maps every
// chemistry into. Ordered worst..best so numeric comparison works ("<= LOW" is
// low-or-worse). UNKNOWN when the sense is unavailable.
typedef enum {
    BATT_BAND_CRITICAL = 0,
    BATT_BAND_LOW      = 1,
    BATT_BAND_GOOD     = 2,
    BATT_BAND_FULL     = 3,
    BATT_BAND_UNKNOWN  = 4,
} batt_band_t;

// A battery snapshot for the active chemistry (settings.batt_chem) and operating
// mode. comp_mv is the load-compensated (mode-normalized) voltage the band/pct
// are derived from; pct is 0..100 only for chemistries with a meaningful percent
// (alkaline), else -1 (NiMH/LiPo report a band, not a fake percent).
typedef struct {
    int         vbat_mv;   // raw sensed VBAT (loaded), or -1 if unavailable
    int         comp_mv;   // load-compensated voltage, or -1
    batt_band_t band;
    int         pct;       // 0..100, or -1 when this chemistry has no percent
    uint8_t     chem;      // batt_chem_t the snapshot was computed for
} batt_status_t;

// Take a fresh battery snapshot (does one VBAT read + maps it through the current
// chemistry model). Cheap enough for a BLE read/notify; stateless (no chime/latch
// side effects — that lives in app_sm_batt_check).
void app_sm_batt_status(batt_status_t *out);

// Short human name for a band ("Full"/"Good"/"Low"/"Critical"/"--").
const char *app_sm_batt_band_name(batt_band_t band);

// Periodic battery poll (call from the ~60 s heartbeat): refreshes the meter,
// logs VBAT/band, and drives the low-power chime with median smoothing + a
// confirm count + a downward-crossing latch so transient load dips never false-
// trigger. No-op chime in Mode A (the battery-saver mode, DSP path stopped).
void app_sm_batt_check(void);
